fernarau9652/Embedded-Systems-Project/STM32/5780-6780-Final-Project3/Core/Inc/i2c.h

void initI2C(void);
void PrepareI2C2Transaction(__UINT32_TYPE__ address, char RD_WRN, int numbytes);
void TransmissionWriteHelper(__UINT32_TYPE__ address, int numbytes, __UINT32_TYPE__ data);
char TransmissionReadHelper(__UINT32_TYPE__ address, int numbytes);
